andres-garcia-alves/electronics-laboratory-psu-lm2596-module/Resources/07-case-3d-model-03.jpg

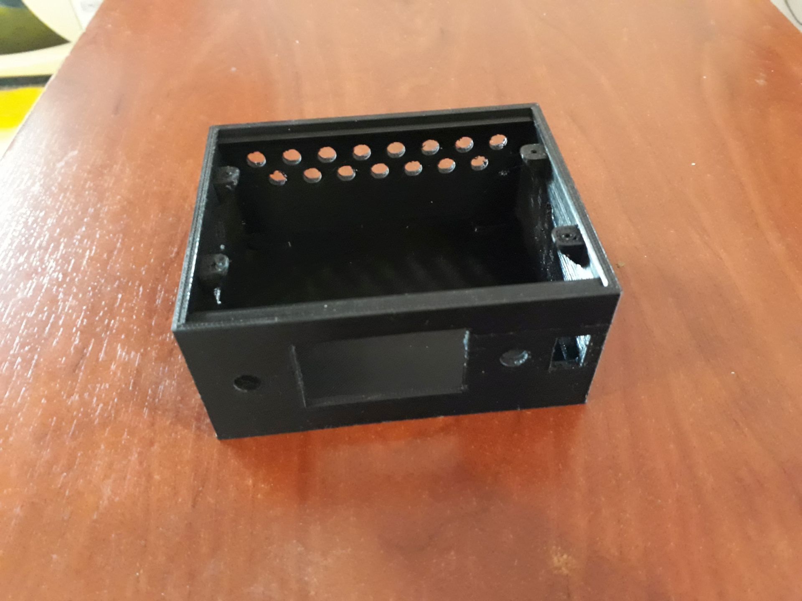
Resources/07-case-3d-model-03.jpg
